Panko74/Simple-CW-Keyer/Circuit diagrams/Diagram.kicad_sch

## KiCad design Circuit diagrams/Diagram.kicad_sch (2026-05-07)

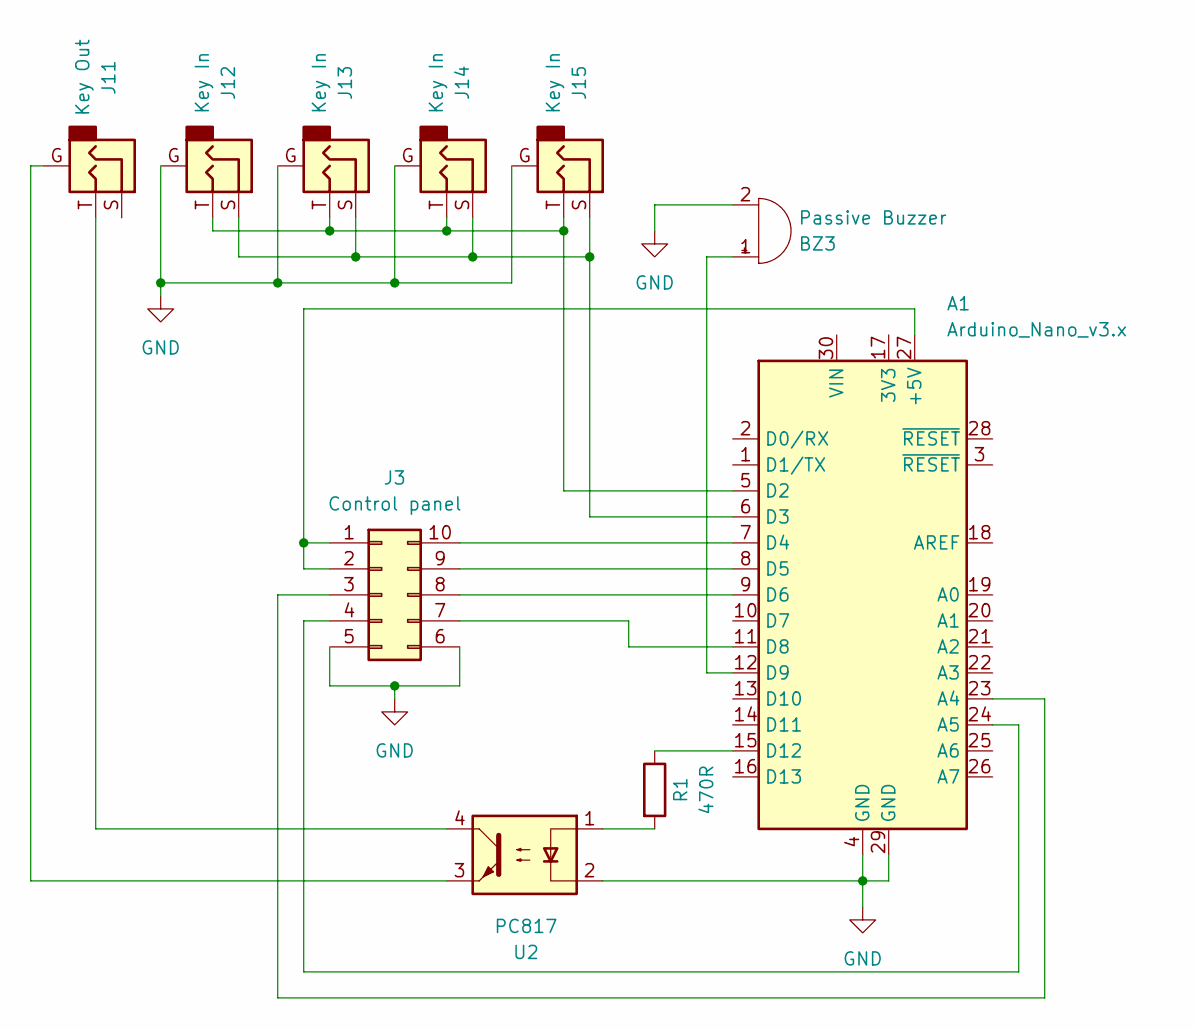
[picture p3: schematic Diagram.kicad_sch]

Parts:
A1: Arduino_Nano_v3.x; Arduino_Nano
BZ3: Passive Buzzer; Buzzer_12x9.5RM7.6
J3: Control panel; PinHeader_2x05_P2.54mm_Vertical
J11: Key Out; Jack_3.5mm_CUI_SJ1-3513N_Horizontal
J12, J13, J14, J15: Key In; Jack_3.5mm_CUI_SJ1-3513N_Horizontal
R1: 470R; R_Axial_DIN0207_L6.3mm_D2.5mm_P10.16mm_Horizontal
U2: PC817; DIP-4_W7.62mm

Connections:
GND: A1.4 (GND), A1.29 (GND), BZ3.2 (-), J3.5, J3.6, J12.G, J13.G, J14.G, J15.G, U2.2
unnamed: A1.5 (D2), J12.T, J13.T, J14.T, J15.T
unnamed: A1.6 (D3), J12.S, J13.S, J14.S, J15.S
unnamed: A1.7 (D4), J3.10
unnamed: A1.8 (D5), J3.9
unnamed: A1.9 (D6), J3.8
unnamed: A1.11 (D8), J3.7
unnamed: A1.12 (D9), BZ3.1 (+)
unnamed: A1.15 (D12), R1.1
unnamed: A1.23 (A4), J3.3
unnamed: A1.24 (A5), J3.4
unnamed: A1.27 (+5V), J3.1, J3.2
unnamed: J11.G, U2.3
unnamed: J11.T, U2.4
unnamed: R1.2, U2.1
